iamjustinkern/Analog-One-Euro-Filter-PCB-Design/1Euro.asc

C1: cap; 10n
C2: cap; 1µ
C3: cap; 100n
D1: diode
D2: diode
R1: res; 10k
R2: res; 1k
R3: res; 1k
R4: res; 47k
R5: res; 20k
R6: res; 20k
R7: res; 10k
R8: res; 20k
R9: res; 20k
R10: res; 30k
R11: res; 100k
R12: res; 10k
R13: res; 10k
R14: res; 10k
R15: res; 20k
R16: res; 1k
R17: res; 1k
U1: LT1228
U2: AD713
U3: AD713
U4: AD713
U5: AD713
U6: AD713
V1: voltage; SINE(0 , 0.1, 1000)
V2: voltage; +5
V3: voltage; 5
V8: voltage; +5
Named nets: V_control, V3, 0, V2, V_in, V_vel, V_fc, Min_Cutoff_Freq, Vel_Sensitivty_Ceoff, Vout, In-
.tran 0 150m 0 10u
